AirPure/AirPure/airpure/src/main/webapp/resources/images/attetion.png

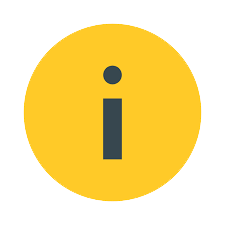
airpure/src/main/webapp/resources/images/attetion.png
