AirPure/AirPure/airpure/src/main/webapp/resources/images/bad.png

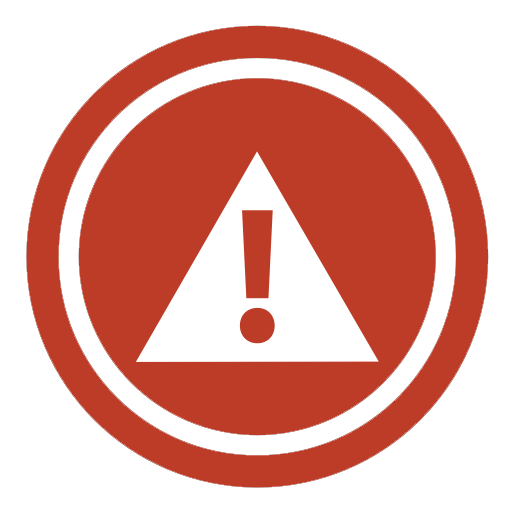
airpure/src/main/webapp/resources/images/bad.png
