AirPure/AirPure/airpure/src/main/webapp/resources/images/foto_.png

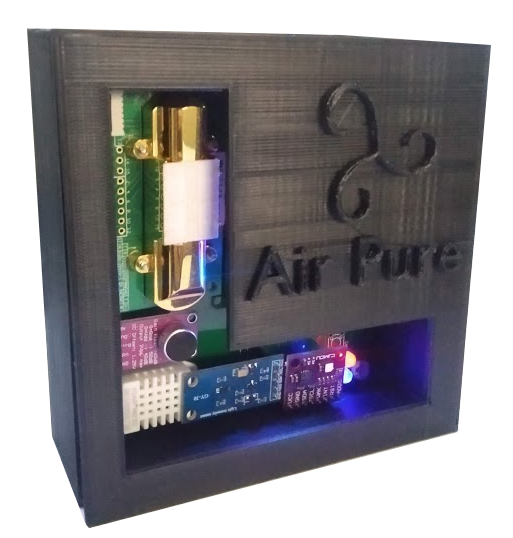
airpure/src/main/webapp/resources/images/foto_.png
