AirPure/AirPure/Diagrama de Ligação/Arquivos/PCB_PCB_AIRPURE_2021-03-10.png

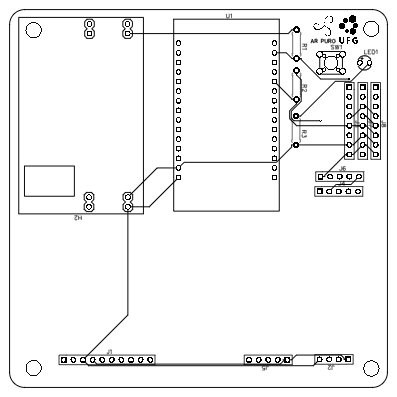
Diagrama de Ligação/Arquivos/PCB_PCB_AIRPURE_2021-03-10.png
