AirPure/AirPure/Diagrama de Ligação/Arquivos/tabela.png

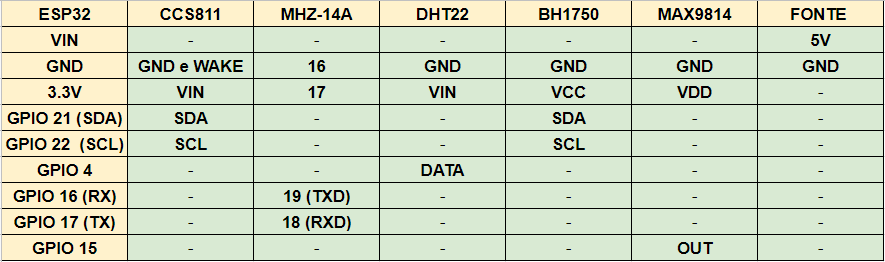
Diagrama de Ligação/Arquivos/tabela.png
