AirPure/AirPure/Diagrama de Ligação/esquemático.png

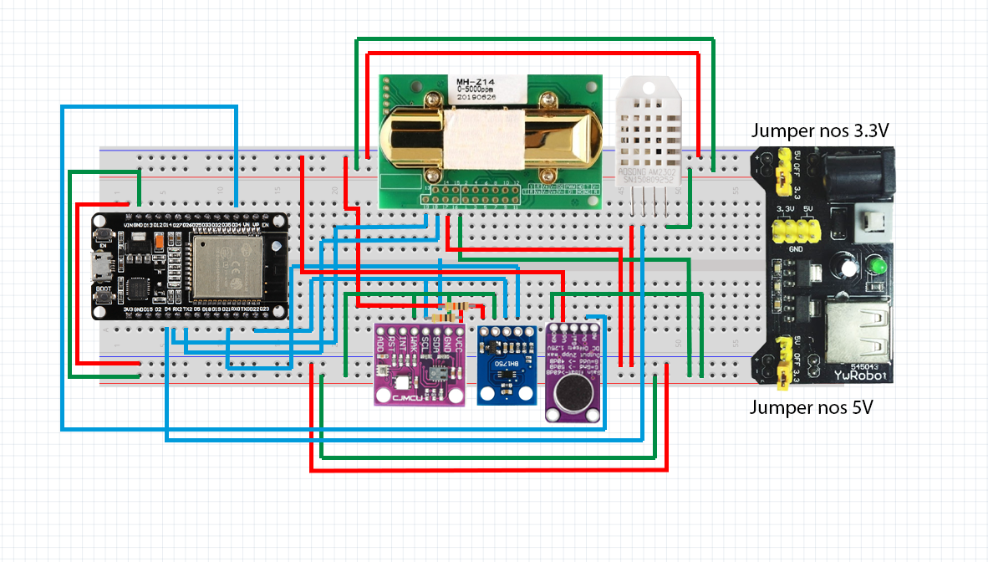
Diagrama de Ligação/esquemático.png
