AirPure/AirPure/Landing Page/assets/img/1.jpg

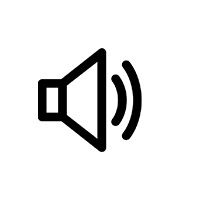
Landing Page/assets/img/1.jpg
