AirPure/AirPure/Landing Page/assets/img/2.jpg

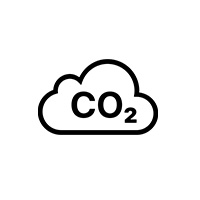
Landing Page/assets/img/2.jpg
