AirPure/AirPure/Landing Page/assets/img/3.jpg

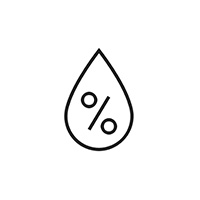
Landing Page/assets/img/3.jpg
