AirPure/AirPure/Landing Page/assets/img/5.jpg

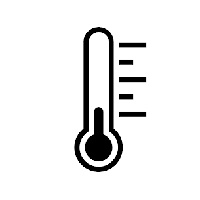
Landing Page/assets/img/5.jpg
