AirPure/AirPure/Landing Page/assets/img/6.jpg

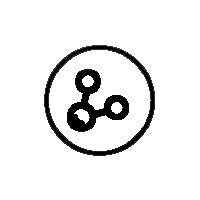
Landing Page/assets/img/6.jpg
