AirPure/AirPure/Landing Page/assets/img/angular.jpg

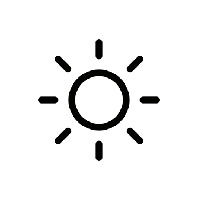
Landing Page/assets/img/angular.jpg
