AirPure/AirPure/Landing Page/assets/img/documentation.png

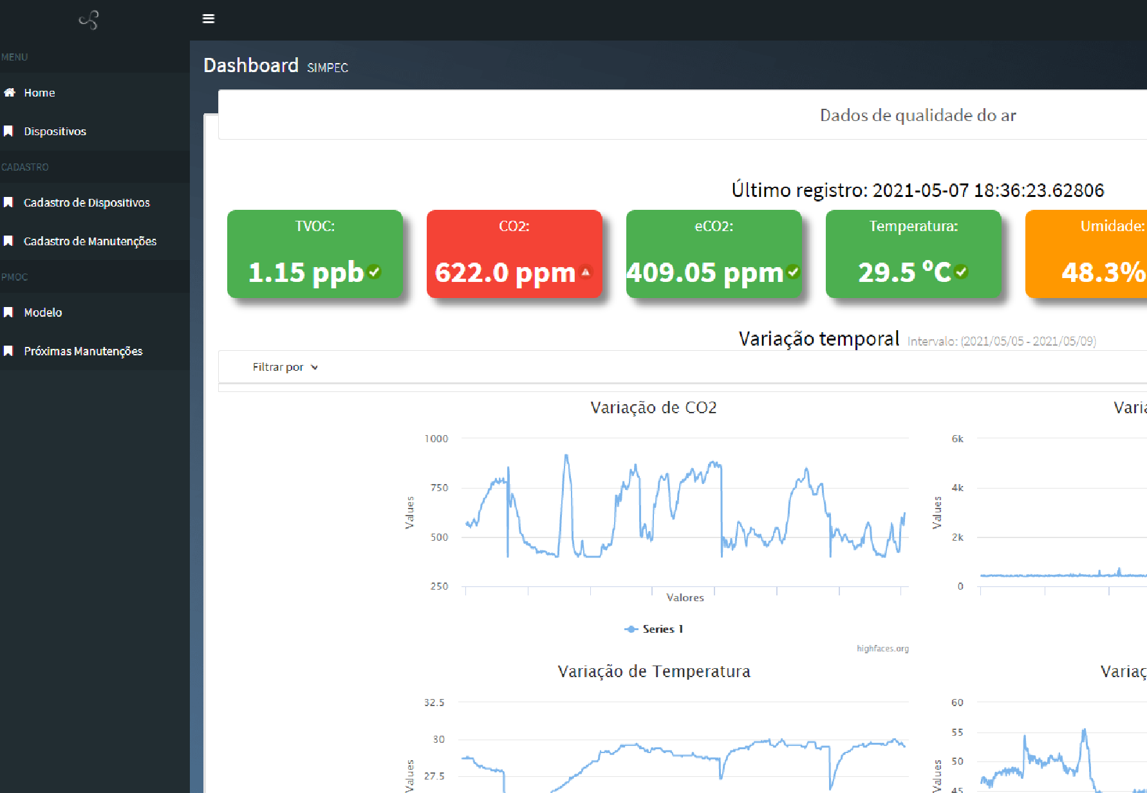
Landing Page/assets/img/documentation.png
