AirPure/AirPure/Landing Page/assets/img/pattern_nextjs.png

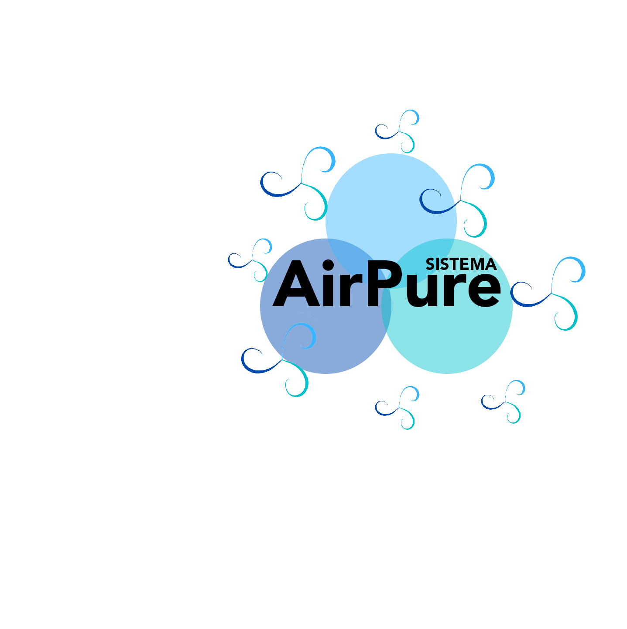
Landing Page/assets/img/pattern_nextjs.png
