AirPure/AirPure/Diagrama de Ligação/Arquivos/hexagon_sheet_3.stl

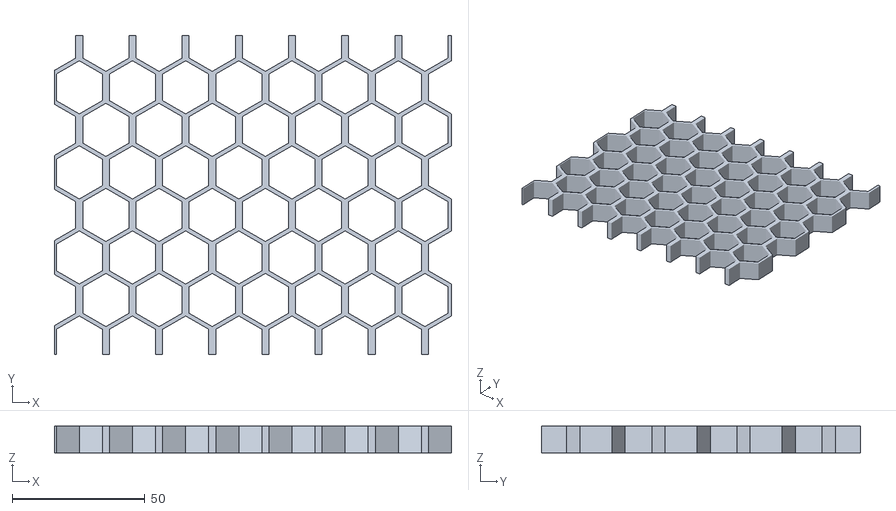
[picture p53: CAD file, 2021-03-12]
Diagrama de Ligação/Arquivos/hexagon_sheet_3.stl
149.3 x 120.0 x 10.0
