AirPure/AirPure/Diagrama de Ligação/Arquivos/untitled.stl

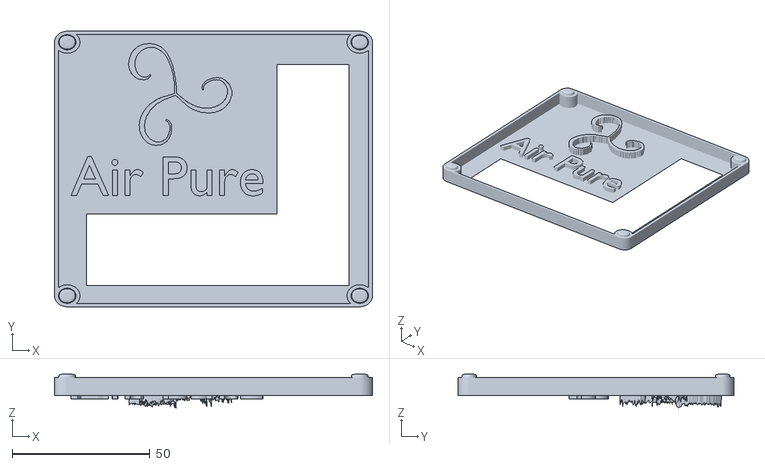
[picture p54: CAD file, 2021-03-12]
Diagrama de Ligação/Arquivos/untitled.stl
115.4 x 100.0 x 12.2
