AirPure/AirPure/Diagrama de Ligação/Arquivos/OBJ_PCB_AIRPURE.stl

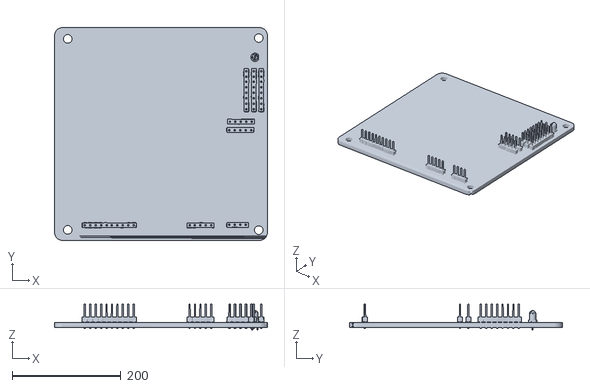
[picture p55: CAD file, 2021-03-12]
Diagrama de Ligação/Arquivos/OBJ_PCB_AIRPURE.stl
392.5 x 392.5 x 47.1
