AirPure/AirPure/Diagrama de Ligação/Arquivos/b100x100x25v1.stl

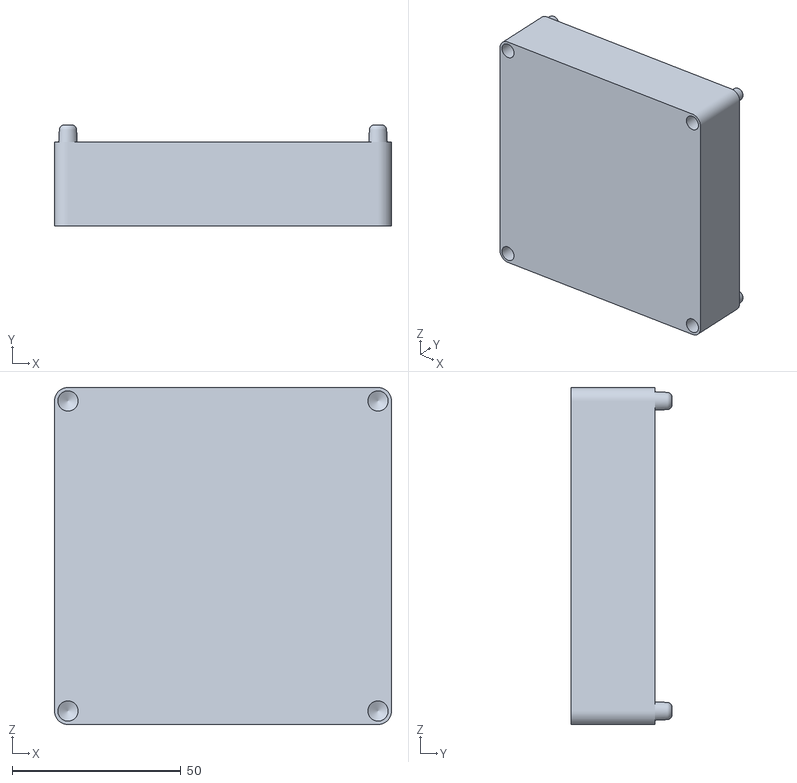
[picture p56: CAD file, 2021-03-12]
Diagrama de Ligação/Arquivos/b100x100x25v1.stl
100.0 x 30.0 x 100.0
