AirPure/AirPure/Diagrama de Ligação/Arquivos/untitledbase.stl

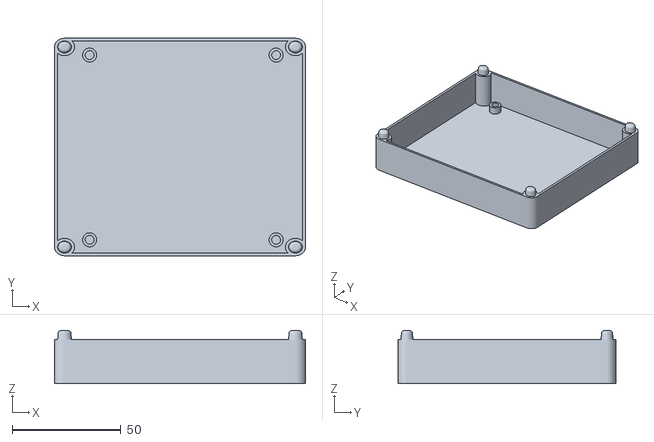
[picture p57: CAD file, 2021-03-12]
Diagrama de Ligação/Arquivos/untitledbase.stl
115.4 x 100.0 x 24.4
