AirPure/AirPure/Diagrama de Ligação/Arquivos/pcb_pcb_airpure_2021-03-10.stl

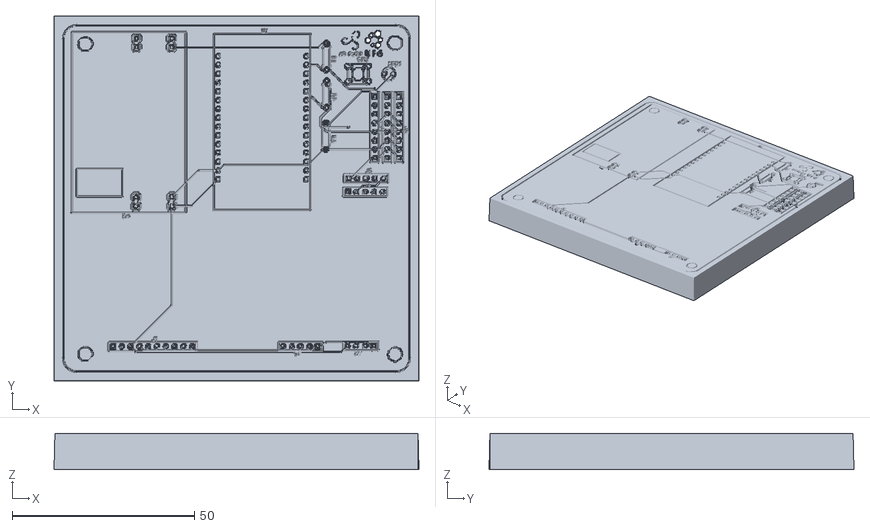
[picture p58: CAD file, 2021-03-12]
Diagrama de Ligação/Arquivos/pcb_pcb_airpure_2021-03-10.stl
100.3 x 100.3 x 10.0
