AirPure/AirPure/Diagrama de Ligação/Arquivos/sem título.stl

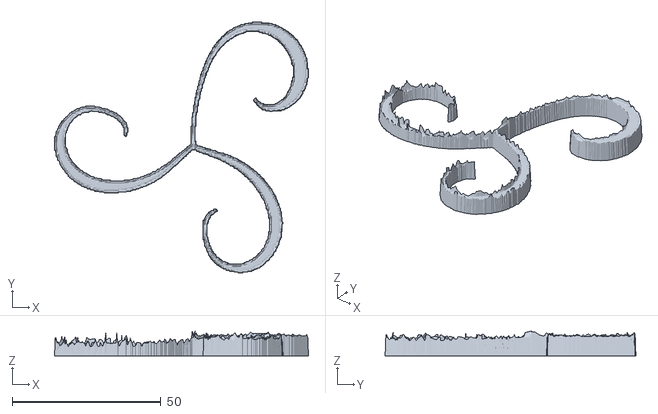
[picture p59: CAD file, 2021-03-12]
Diagrama de Ligação/Arquivos/sem título.stl
85.5 x 84.4 x 8.31
