AirPure/AirPure/Diagrama de Ligação/Arquivos/airpure_case.stl

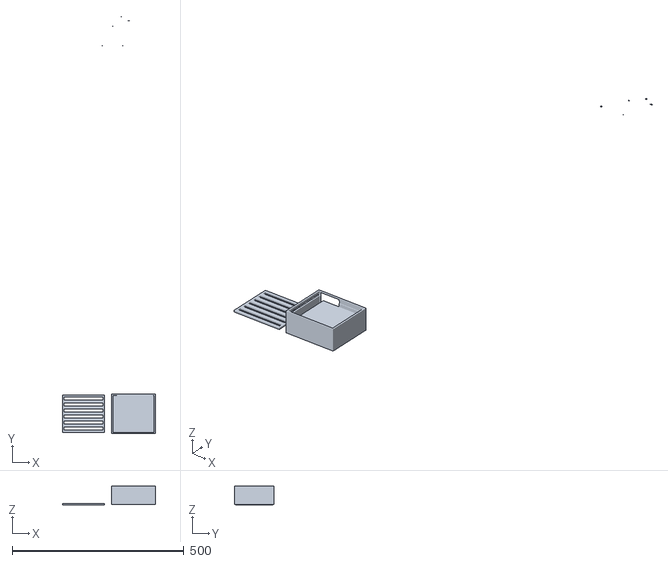
[picture p60: CAD file, 2021-02-21]
Diagrama de Ligação/Arquivos/airpure_case.stl
270.6 x 1213.5 x 54.6
