AirPure/AirPure/Diagrama de Ligação/Arquivos/PCB_AIRPURE_2021-02-21.dxf

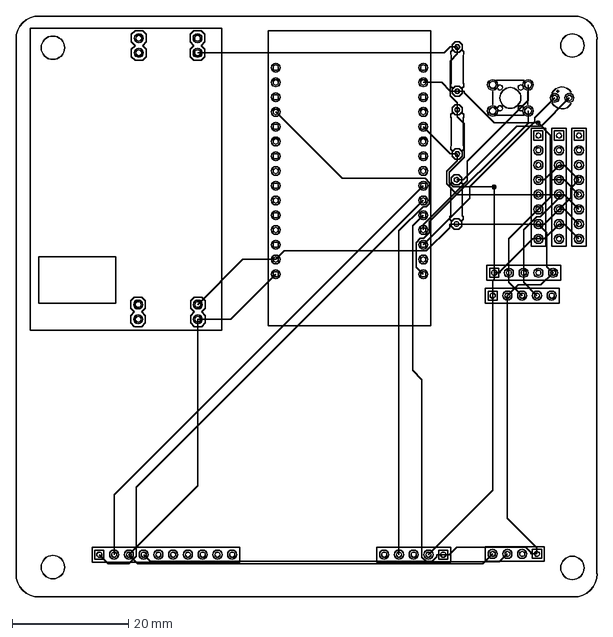
[picture p61: CAD file, 2021-02-21]
Diagrama de Ligação/Arquivos/PCB_AIRPURE_2021-02-21.dxf
100.0 x 100.0 mm
