AirPure/AirPure/Codigo/air_pure_geral/air_pure/globalvar.h

/*
O AirPure é um dispositivo embarcado para análise de qualidade do ar.
Seu código atualmente é mantido por professores e estudantes da UFG.
Confira nosso repositório no GitHub: https://github.com/AirPure/AirPure
*/

const char * root_ca=\
"-----BEGIN CERTIFICATE-----\n" \
"MIIDujCCAqKgAwIBAgILBAAAAAABD4Ym5g0wDQYJKoZIhvcNAQEFBQAwTDEgMB4G\n" \
"A1UECxMXR2xvYmFsU2lnbiBSb290IENBIC0gUjIxEzARBgNVBAoTCkdsb2JhbFNp\n" \
"Z24xEzARBgNVBAMTCkdsb2JhbFNpZ24wHhcNMDYxMjE1MDgwMDAwWhcNMjExMjE1\n" \
"MDgwMDAwWjBMMSAwHgYDVQQLExdHbG9iYWxTaWduIFJvb3QgQ0EgLSBSMjETMBEG\n" \
"A1UEChMKR2xvYmFsU2lnbjETMBEGA1UEAxMKR2xvYmFsU2lnbjCCASIwDQYJKoZI\n" \
"hvcNAQEBBQADggEPADCCAQoCggEBAKbPJA6+Lm8omUVCxKs+IVSbC9N/hHD6ErPL\n" \
"v4dfxn+G07IwXNb9rfF73OX4YJYJkhD10FPe+3t+c4isUoh7SqbKSaZeqKeMWhG8\n" \
"eoLrvozps6yWJQeXSpkqBy+0Hne/ig+1AnwblrjFuTosvNYSuetZfeLQBoZfXklq\n" \
"tTleiDTsvHgMCJiEbKjNS7SgfQx5TfC4LcshytVsW33hoCmEofnTlEnLJGKRILzd\n" \
"C9XZzPnqJworc5HGnRusyMvo4KD0L5CLTfuwNhv2GXqF4G3yYROIXJ/gkwpRl4pa\n" \
"zq+r1feqCapgvdzZX99yqWATXgAByUr6P6TqBwMhAo6CygPCm48CAwEAAaOBnDCB\n" \
"mTAOBgNVHQ8BAf8EBAMCAQYwDwYDVR0TAQH/BAUwAwEB/zAdBgNVHQ4EFgQUm+IH\n" \
"V2ccHsBqBt5ZtJot39wZhi4wNgYDVR0fBC8wLTAroCmgJ4YlaHR0cDovL2NybC5n\n" \
"bG9iYWxzaWduLm5ldC9yb290LXIyLmNybDAfBgNVHSMEGDAWgBSb4gdXZxwewGoG\n" \
"3lm0mi3f3BmGLjANBgkqhkiG9w0BAQUFAAOCAQEAmYFThxxol4aR7OBKuEQLq4Gs\n" \
"J0/WwbgcQ3izDJr86iw8bmEbTUsp9Z8FHSbBuOmDAGJFtqkIk7mpM0sYmsL4h4hO\n" \
"291xNBrBVNpGP+DTKqttVCL1OmLNIG+6KYnX3ZHu01yiPqFbQfXf5WRDLenVOavS\n" \
"ot+3i9DAgBkcRcAtjOj4LaR0VknFBbVPFd5uRHg5h6h+u/N5GJG79G+dwfCMNYxd\n" \
"AfvDbbnvRG15RjF+Cv6pgsH/76tuIMRQyV+dTZsXjAzlAcmgQWpzU/qlULRuJQ/7\n" \
"TBj0/VLZjmmx6BEP3ojY+x1J96relc8geMJgEtslQIxq/H5COEBkEveegeGTLg==\n" \
"-----END CERTIFICATE-----\n";

char* test_root_ca= \
     "-----BEGIN CERTIFICATE-----\n"  
  "MIIDxTCCAq2gAwIBAgIQAqxcJmoLQJuPC3nyrkYldzANBgkqhkiG9w0BAQUFADBsMQswCQYDVQQG\n"  
  "EwJVUzEVMBMGA1UEChMMRGlnaUNlcnQgSW5jMRkwFwYDVQQLExB3d3cuZGlnaWNlcnQuY29tMSsw\n"  
  "KQYDVQQDEyJEaWdpQ2VydCBIaWdoIEFzc3VyYW5jZSBFViBSb290IENBMB4XDTA2MTExMDAwMDAw\n"  
  "MFoXDTMxMTExMDAwMDAwMFowbDELMAkGA1UEBhMCVVMxFTATBgNVBAoTDERpZ2lDZXJ0IEluYzEZ\n"  
  "MBcGA1UECxMQd3d3LmRpZ2ljZXJ0LmNvbTErMCkGA1UEAxMiRGlnaUNlcnQgSGlnaCBBc3N1cmFu\n"  
  "Y2UgRVYgUm9vdCBDQTCCASIwDQYJKoZIhvcNAQEBBQADggEPADCCAQoCggEBAMbM5XPm+9S75S0t\n"  
  "Mqbf5YE/yc0lSbZxKsPVlDRnogocsF9ppkCxxLeyj9CYpKlBWTrT3JTWPNt0OKRKzE0lgvdKpVMS\n"  
  "OO7zSW1xkX5jtqumX8OkhPhPYlG++MXs2ziS4wblCJEMxChBVfvLWokVfnHoNb9Ncgk9vjo4UFt3\n"  
  "MRuNs8ckRZqnrG0AFFoEt7oT61EKmEFBIk5lYYeBQVCmeVyJ3hlKV9Uu5l0cUyx+mM0aBhakaHPQ\n"  
  "NAQTXKFx01p8VdteZOE3hzBWBOURtCmAEvF5OYiiAhF8J2a3iLd48soKqDirCmTCv2ZdlYTBoSUe\n"  
  "h10aUAsgEsxBu24LUTi4S8sCAwEAAaNjMGEwDgYDVR0PAQH/BAQDAgGGMA8GA1UdEwEB/wQFMAMB\n"  
  "Af8wHQYDVR0OBBYEFLE+w2kD+L9HAdSYJhoIAu9jZCvDMB8GA1UdIwQYMBaAFLE+w2kD+L9HAdSY\n"  
  "JhoIAu9jZCvDMA0GCSqGSIb3DQEBBQUAA4IBAQAcGgaX3NecnzyIZgYIVyHbIUf4KmeqvxgydkAQ\n"  
  "V8GK83rZEWWONfqe/EW1ntlMMUu4kehDLI6zeM7b41N5cdblIZQB2lWHmiRk9opmzN6cN82oNLFp\n"  
  "myPInngiK3BD41VHMWEZ71jFhS9OMPagMRYjyOfiZRYzy78aG6A9+MpeizGLYAiJLQwGXFK3xPkK\n"  
  "mNEVX58Svnw2Yzi9RKR/5CYrCsSXaQ3pjOLAEFe4yHYSkVXySGnYvCoCWw9E1CAx2/S6cCZdkGCe\n"  
  "vEsXCS+0yx5DaMkHJ8HSXPfqIbloEpw8nL+e/IBcm2PN7EeqJSdnoDfzAIJ9VNep+OkuE6N36B9K\n" 
  "-----END CERTIFICATE-----\n" ;

  const char* eduroam_root_ca= \
"-----BEGIN CERTIFICATE-----\n" \
"MIIDrzCCApegAwIBAgIQCDvgVpBCRrGhdWrJWZHHSjANBgkqhkiG9w0BAQUFADBh\n" \
"MQswCQYDVQQGEwJVUzEVMBMGA1UEChMMRGlnaUNlcnQgSW5jMRkwFwYDVQQLExB3\n" \
"d3cuZGlnaWNlcnQuY29tMSAwHgYDVQQDExdEaWdpQ2VydCBHbG9iYWwgUm9vdCBD\n" \
"QTAeFw0wNjExMTAwMDAwMDBaFw0zMTExMTAwMDAwMDBaMGExCzAJBgNVBAYTAlVT\n" \
"MRUwEwYDVQQKEwxEaWdpQ2VydCBJbmMxGTAXBgNVBAsTEHd3dy5kaWdpY2VydC5j\n" \
"b20xIDAeBgNVBAMTF0RpZ2lDZXJ0IEdsb2JhbCBSb290IENBMIIBIjANBgkqhkiG\n" \
"9w0BAQEFAAOCAQ8AMIIBCgKCAQEA4jvhEXLeqKTTo1eqUKKPC3eQyaKl7hLOllsB\n" \
"CSDMAZOnTjC3U/dDxGkAV53ijSLdhwZAAIEJzs4bg7/fzTtxRuLWZscFs3YnFo97\n" \
"nh6Vfe63SKMI2tavegw5BmV/Sl0fvBf4q77uKNd0f3p4mVmFaG5cIzJLv07A6Fpt\n" \
"43C/dxC//AH2hdmoRBBYMql1GNXRor5H4idq9Joz+EkIYIvUX7Q6hL+hqkpMfT7P\n" \
"T19sdl6gSzeRntwi5m3OFBqOasv+zbMUZBfHWymeMr/y7vrTC0LUq7dBMtoM1O/4\n" \
"gdW7jVg/tRvoSSiicNoxBN33shbyTApOB6jtSj1etX+jkMOvJwIDAQABo2MwYTAO\n" \
"BgNVHQ8BAf8EBAMCAYYwDwYDVR0TAQH/BAUwAwEB/zAdBgNVHQ4EFgQUA95QNVbR\n" \
"TLtm8KPiGxvDl7I90VUwHwYDVR0jBBgwFoAUA95QNVbRTLtm8KPiGxvDl7I90VUw\n" \
"DQYJKoZIhvcNAQEFBQADggEBAMucN6pIExIK+t1EnE9SsPTfrgT1eXkIoyQY/Esr\n" \
"hMAtudXH/vTBH1jLuG2cenTnmCmrEbXjcKChzUyImZOMkXDiqw8cvpOp/2PV5Adg\n" \
"06O/nVsJ8dWO41P0jmP6P6fbtGbfYmbW0W5BjfIttep3Sp+dWOIrWcBAI+0tKIJF\n" \
"PnlUkiaY4IBIqDfv8NZ5YBberOgOzW6sRBc4L0na4UU+Krk2U886UAb3LujEV0ls\n" \
"YSEY1QSteDwsOoBrp+uvFRTp2InBuThs4pFsiv9kuXclVzDAGySj4dzp30d8tbQk\n" \
"CAUw7C29C79Fv1C5qfPrmAESrciIxpg0X40KPMbp1ZWVbd4=\n" \
"-----END CERTIFICATE-----\n";

/*Variáveis*/
float temp; //Temperatura em graus celsius.
float umid; //Umidade relativa.
uint16_t lux; //Valor em Lux referente à luminosidade.
float eco2, eco2Sum; //Equivalente de Dióxido de carbono.
float voc, vocSum; //Total de compostos organicos voláteis.
float valorCO2; //Dióxido de carbono. 
float dbLevel; //Valor em DB de ruído do ambiente
int highCO2 = 0; //Flag de alto indice de CO2.
int timeOutReading = 30;  //Timeout de leitura
int timeoutHorario = 30;  //Timeout para obter hora
int r = 0; //Variável de retorno de funções
String formattedDate; //String para receber o horário.
int isWaitingForOta = 0; //Flag que houve uma conexao via OTA.
char mqttUserName[] = "airpure"; //nome de usuário do MQTT
char mqttPass[] = "0QIMS6VELRQUUC0A"; //chave de acesso do MQTT.
char homeassistant_mqtt_user[] = "airpure"; //nome de usuário do MQTT
char homeassistant_mqtt_pass[] = "airpure"; //chave de acesso do MQTT.
String writeAPIKey[3] = {"WDPPXX2EI7II24E0","EB6J5ATU4ETP7984","W1OE6ARR4S0X2OAT"}; //chave de escrita, canal Thingspeak.
String GOOGLE_SCRIPT_ID[3] = {"AKfycbyTjkzdpp9rY3XtslFZvW5jxvUnXPAYHTeV4eMmk4uSXMNe5DXV","AKfycbyc1aXXiS_7kK6o7It_4Bit2T4Y8Ub1Un-ofFATPdNSCKDwmmz6","AKfycbyLI0hLaPGFe7XIY6012YkjHCZeKCEcrg0FifhmsBEY2QaRXszV"}; //Google Sheets
long channelID[3] = {1160801,1167146,1177969}; //Identificação do canal Thingspeak - Pessoal.
static const char alphanum[] = "0123456789""ABCDEFGHIJKLMNOPQRSTUVWXYZ""abcdefghijklmnopqrstuvwxyz"; //Definir identificação de cliente, randomico.
const char* server = "mqtt.thingspeak.com"; //Servidor do MQTT para o ThingSpeak
String umidade_topic = "sensor/umidade/";  //Topicos do MQTT para o HomeAssistant
String temperatura_topic = "sensor/temperatura/";  //Topicos do MQTT para o HomeAssistant
String botao_topic = "sensor/botao/1";  //Topicos do MQTT para o HomeAssistant
String tvoc_topic = "sensor/tvoc/";  //Topicos do MQTT para o HomeAssistant
String co2_topic = "sensor/co2/";  //Topicos do MQTT para o HomeAssistant
String eco2_topic = "sensor/eco2/";  //Topicos do MQTT para o HomeAssistant 
String ruido_topic = "sensor/ruido/";  //Topicos do MQTT para o HomeAssistant
String luminosidade_topic = "sensor/lux/";  //Topicos do MQTT para o HomeAssistant
unsigned long lastConnectionTime = 0; //Tempo da última conexão.
const unsigned long postingInterval = 20000L; //Tempo de postagem, 20 segundos.
const int sampleWindow = 50; // Janela de amostragem em mS (50 mS = 20Hz)
unsigned int sample;  //Variável referente a leitura do sensor de ruído
String input;
int cont = 0; //Contador de pessoas
int AIRPURE_ID;  //Seu ID do airpure
int val = 0; //Variavel auxiliar
long duration1;
int distance1 = 0;
long duration2;
int distance2 = 0;
int estado;
int isContadorPessoas = 0;  
int isSendingAirServer = 0;
int sender = 0; int receiver = 0;
int wifiManager = 0;
const char* ssid = "eduroam"; // Eduroam SSID
int recordCounter = 0;
String valores = "";
const char* ssidLR = "kkkkk";//AP ssid
const char* passwordLR = "12345678";//AP password
const char* ssidRouterLR = "BMS";//STA router ssid
const char* passwordRouterLR = "+556232853960";//STA router password
char  replyPacket[] = "Hi there! Got the message :-)";  // a reply string to send back
int espnow = 0;
int timeoutConnection =  60;
char incomingPacket[255];  // buffer for incoming packets

typedef struct struct_message {
  float a;
  float b;
  int c;
  int d;
  int e;
  int f;
  int g;
  int h;
  String i;
} struct_message;

struct_message myData;
