AirPure/AirPure/Codigo/air_pure_geral/air_pure/prototypes.h

/*
O AirPure é um dispositivo embarcado para análise de qualidade do ar.
Seu código atualmente é mantido por professores e estudantes da UFG.
Confira nosso repositório no GitHub: https://github.com/AirPure/AirPure
*/

/*Bibliotecas*/
#include <PubSubClient.h>
#include <WiFiManager.h>         
#include <BH1750.h>
#include <DHT.h>
#include <WiFi.h>
#include <esp_now.h>
#include <SPI.h>
#include <esp_wifi.h>
#include <Wire.h>
#include <Adafruit_CCS811.h>
#include <i2cdetect.h>
#include <WiFiClientSecure.h>
#include <UniversalTelegramBot.h>
#include <ArduinoJson.h>
#include <NTPClient.h>
#include <WiFiUdp.h>
#include <Arduino.h>
#include "ArduinoNvs.h"
#include <ArduinoOTA.h>
#include <HTTPClient.h>
#include <ESPmDNS.h>
#include <esp32fota.h>
#include <esp_task_wdt.h> 
#include "globalvar.h"
#include "globaldef.h"
#include <Ultrasonic.h>
#include "esp_wpa2.h"



/*Declaração*/
BH1750 lightMeter (0x23); //Sensor de luminosidade - BH1750 (Addr: 0x23)
WiFiClientSecure client2; //Inicializar cliente wifi
WiFiClient client; //Inicializar cliente wifi
UniversalTelegramBot bot(BTKEN, client2); //Instanciando bot do telegram
WiFiUDP ntpUDP; //NTP-UDP
NTPClient timeClient(ntpUDP);//Cliente NTP
DHT dht(dhtPin, dhtType); //Objeto sensor de temperatura e umidade
PubSubClient mqttClient(client);  //ThingSpeak
PubSubClient mqttClient2(client); //HomeAssistant
secureEsp32FOTA secureEsp32FOTA("esp32-fota-https", V_FIRMWARE);
WiFiUDP udp;
Adafruit_CCS811 ccs; //Objeto sensor de TVOC. //Instância do CCS811
struct Button {
  const uint8_t PIN;
  uint32_t numberKeyPresses;
  bool pressed;
};

Button button1 = {18, 0, false};


TaskHandle_t task_low_serial;
TaskHandle_t task_low_led;
TaskHandle_t task_low;
void vLow(void *pvParameters);
void vLowSerial(void *pvParameters);
void vLowLED(void *pvParameters);
void homeassistant_publish(void);
